HO4RLZ-SUDI/X-glove/hardware/cad/v2_masterpiece/esp32c3_oled_case_masterpiece_layout.3mf

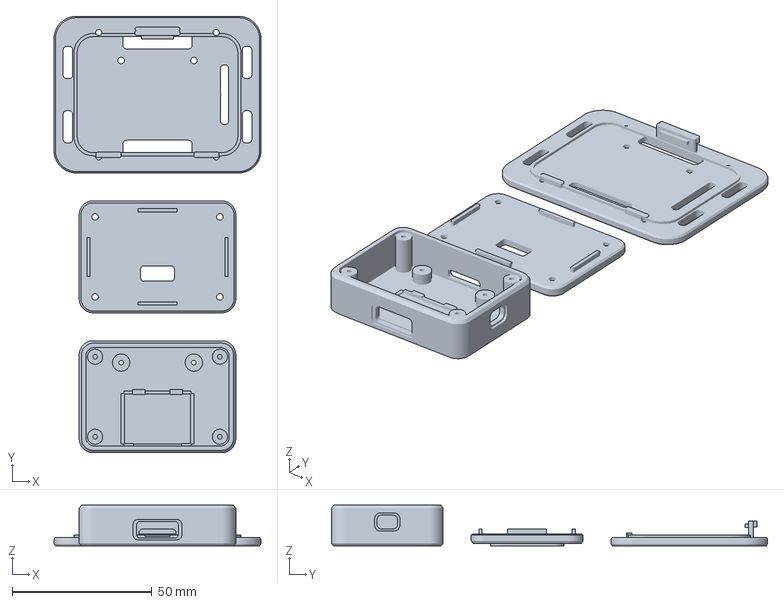
[picture p17: CAD file, 2026-06-17]
hardware/cad/v2_masterpiece/esp32c3_oled_case_masterpiece_layout.3mf
74.0 x 156.0 x 14.5 mm
