HO4RLZ-SUDI/X-glove/hardware/cad/v3_usable/esp32c3_oled_case_usable_mount.stl

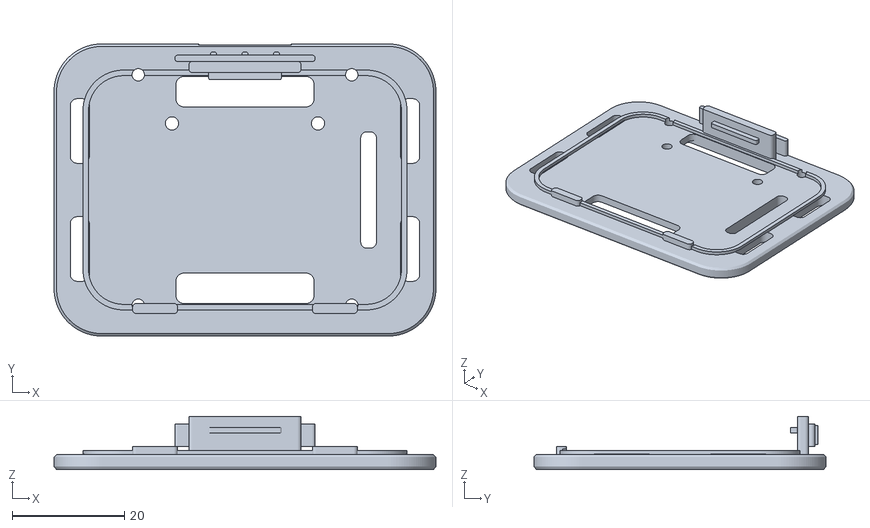
[picture p18: CAD file, 2026-06-17]
hardware/cad/v3_usable/esp32c3_oled_case_usable_mount.stl
68.0 x 52.0 x 9.50
