HO4RLZ-SUDI/X-glove/hardware/watch_case/base.3mf

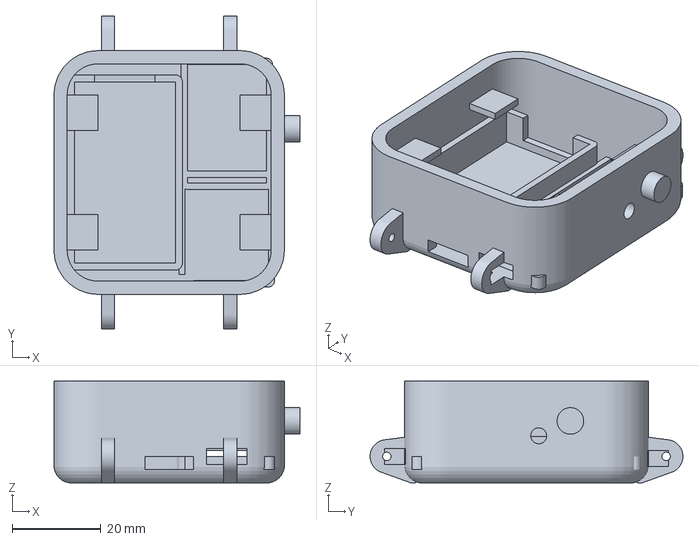
[picture p19: CAD file, 2026-06-27]
hardware/watch_case/base.3mf
55.5 x 70.6 x 23.0 mm
