HO4RLZ-SUDI/X-glove/hardware/cad/v1_oled_case/esp32c3_oled_case_lid.stl

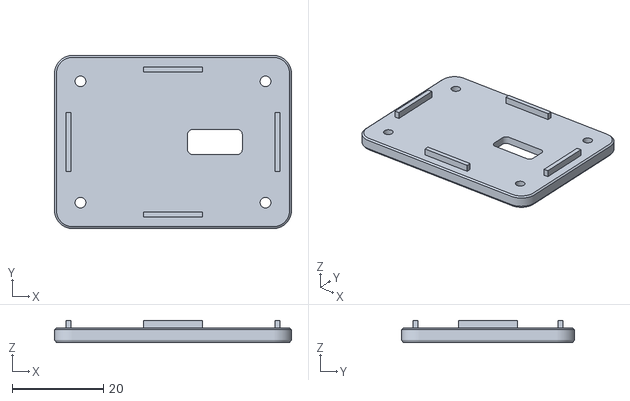
[picture p20: CAD file, 2026-06-17]
hardware/cad/v1_oled_case/esp32c3_oled_case_lid.stl
52.0 x 38.0 x 4.85
