HO4RLZ-SUDI/X-glove/hardware/cad/v2_masterpiece/esp32c3_oled_case_masterpiece_case.stl

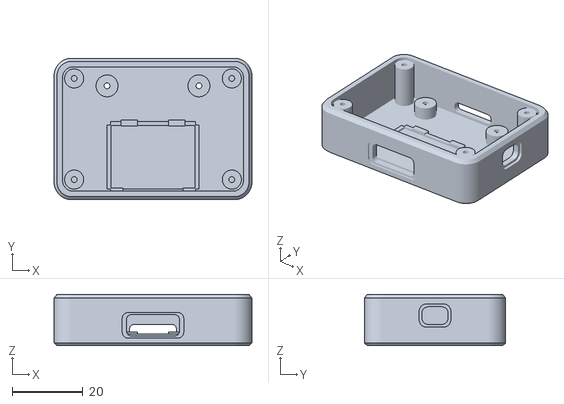
[picture p21: CAD file, 2026-06-17]
hardware/cad/v2_masterpiece/esp32c3_oled_case_masterpiece_case.stl
56.0 x 40.0 x 14.5
