HO4RLZ-SUDI/X-glove/hardware/cad/v3_usable/esp32c3_oled_case_usable_lid.stl

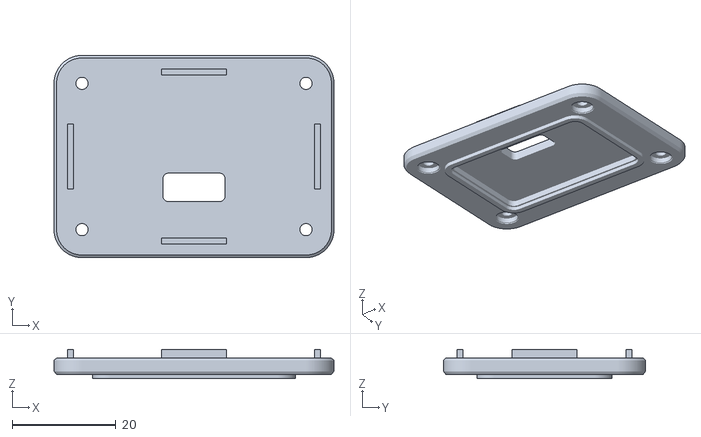
[picture p22: CAD file, 2026-06-17]
hardware/cad/v3_usable/esp32c3_oled_case_usable_lid.stl
54.0 x 39.0 x 5.60
