HO4RLZ-SUDI/X-glove/hardware/cad/v4_comfy/esp32c3_oled_case_comfy_layout.3mf

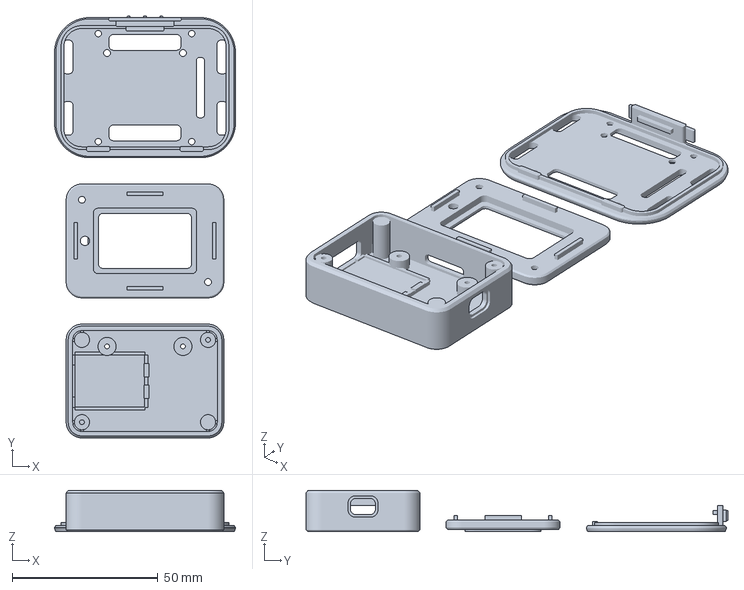
[picture p23: CAD file, 2026-06-17]
hardware/cad/v4_comfy/esp32c3_oled_case_comfy_layout.3mf
62.0 x 144.5 x 14.2 mm
