HO4RLZ-SUDI/X-glove/hardware/cad/v1_oled_case/esp32c3_oled_case_layout.3mf

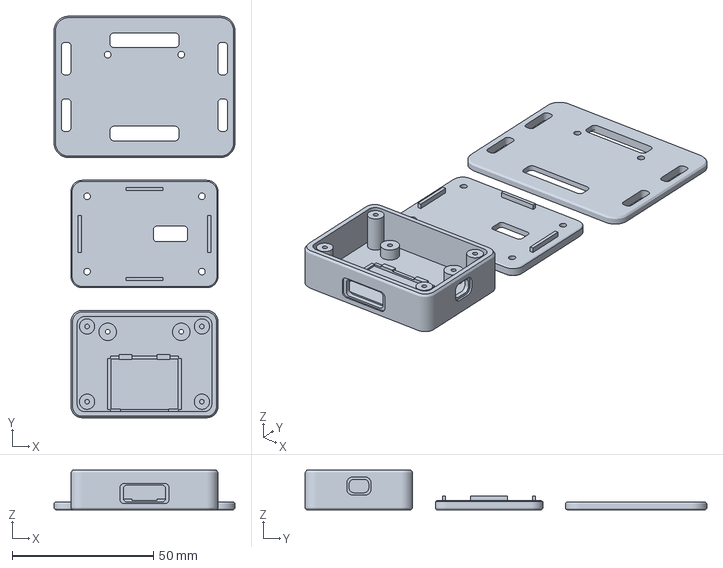
[picture p24: CAD file, 2026-06-17]
hardware/cad/v1_oled_case/esp32c3_oled_case_layout.3mf
64.0 x 142.0 x 14.0 mm
