HO4RLZ-SUDI/X-glove/hardware/cad/v2_masterpiece/esp32c3_oled_case_masterpiece_mount.stl

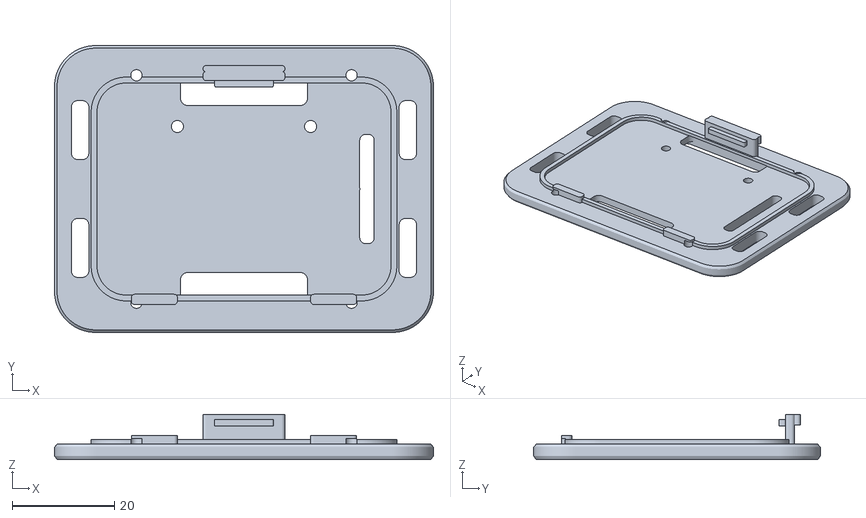
[picture p25: CAD file, 2026-06-17]
hardware/cad/v2_masterpiece/esp32c3_oled_case_masterpiece_mount.stl
74.0 x 56.0 x 8.80
