HO4RLZ-SUDI/X-glove/hardware/cad/v4_comfy/esp32c3_oled_case_comfy_lid.stl

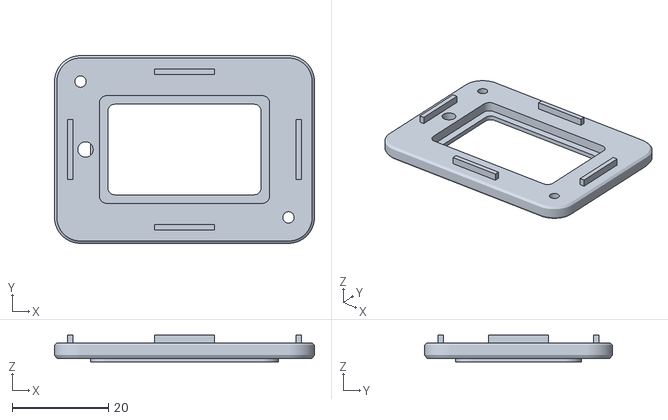
[picture p26: CAD file, 2026-06-17]
hardware/cad/v4_comfy/esp32c3_oled_case_comfy_lid.stl
54.0 x 39.0 x 5.60
